espena/broadcast-clock/drawings/broadcast_clock_back.png

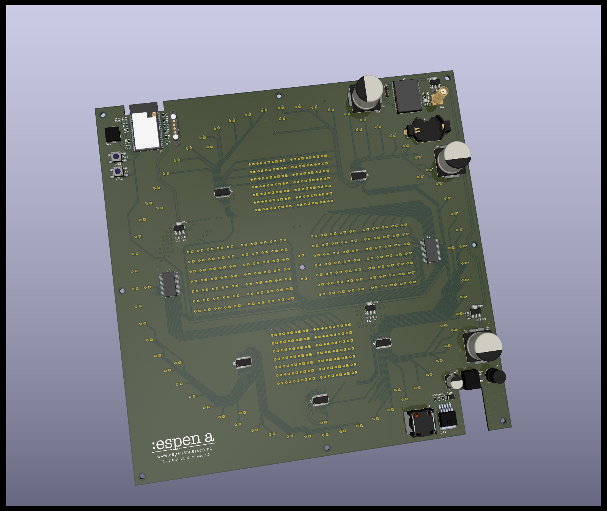
drawings/broadcast_clock_back.png
