espena/broadcast-clock/drawings/broadcast_clock_front.png

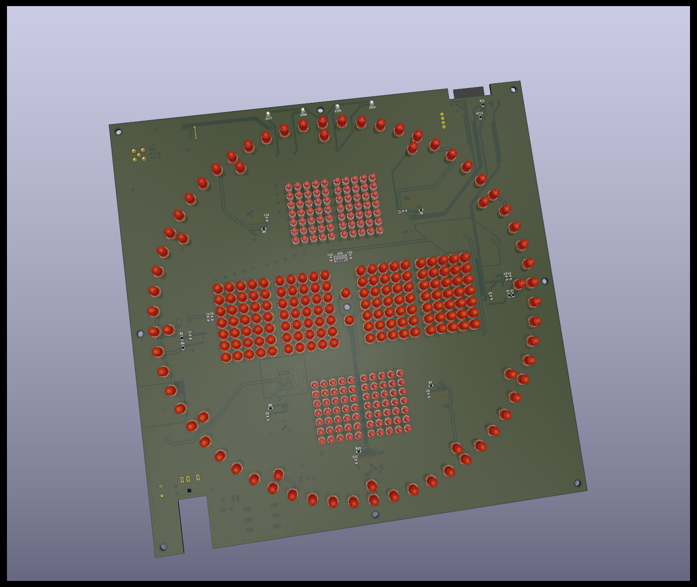
drawings/broadcast_clock_front.png
