espena/broadcast-clock/drawings/kicad_pcb_editor_screencap.png

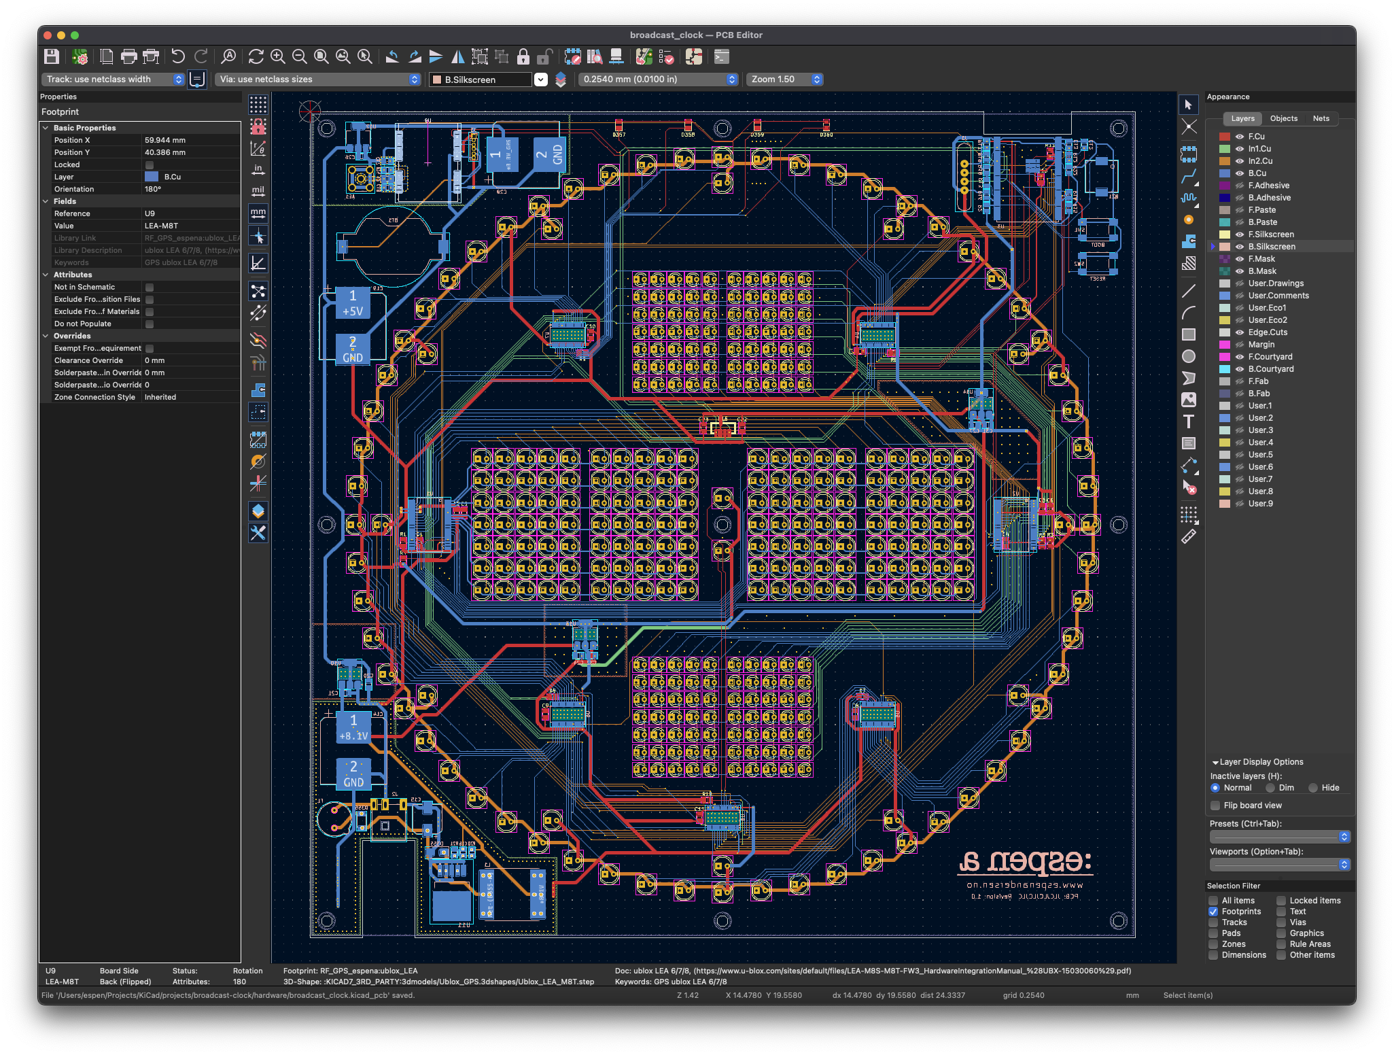
drawings/kicad_pcb_editor_screencap.png
