espena/broadcast-clock/drawings/qcad_panel_design.png

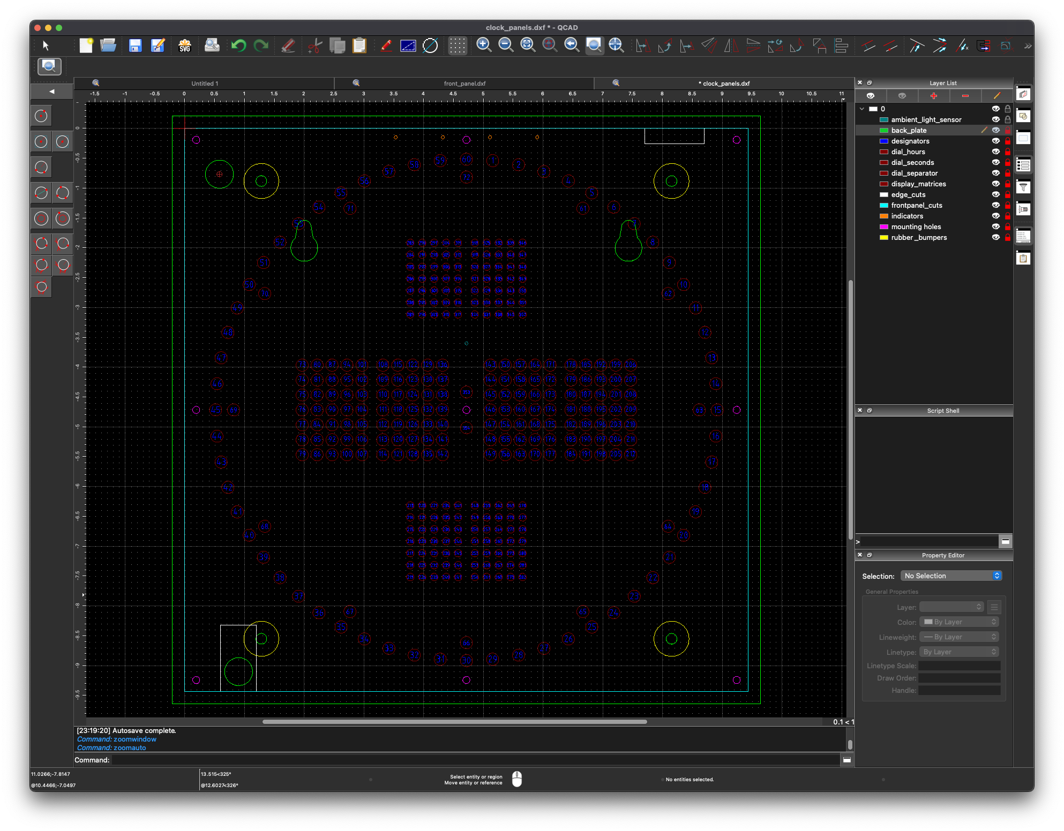
drawings/qcad_panel_design.png
