espena/broadcast-clock/drawings/schematics_png/max6952_schematic.png

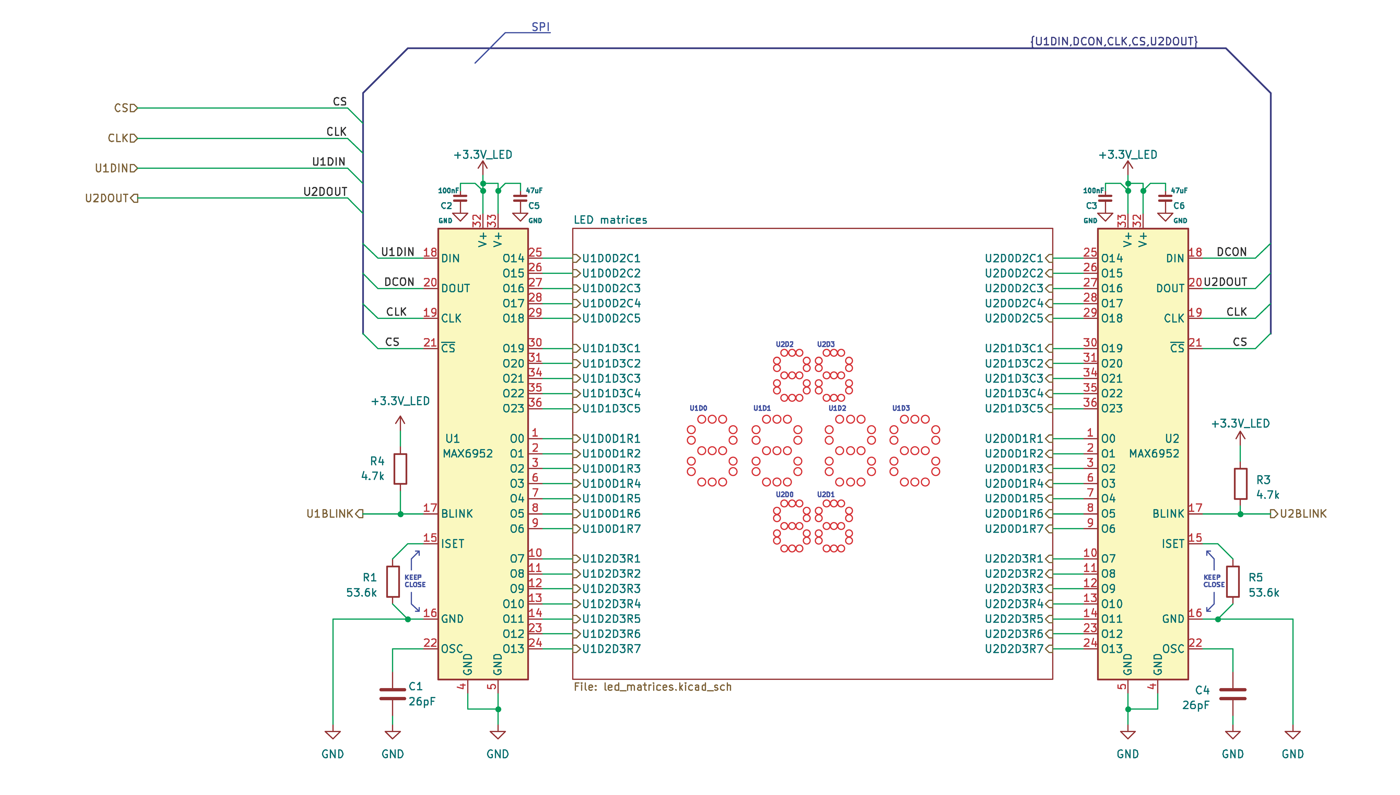
drawings/schematics_png/max6952_schematic.png
