espena/broadcast-clock/drawings/schematics_png/root_schematic.png

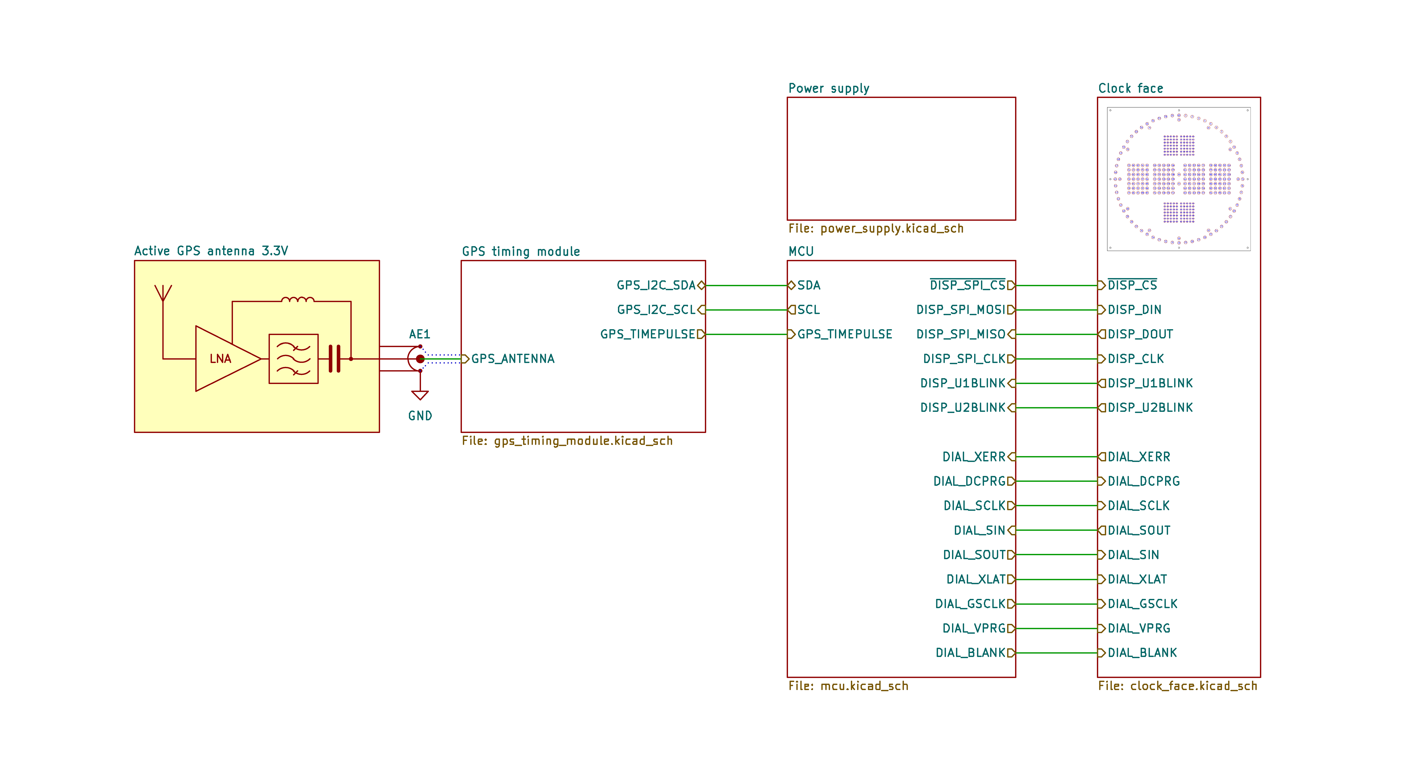
drawings/schematics_png/root_schematic.png
