espena/broadcast-clock/drawings/schematics_png/schematics_Page_3.png

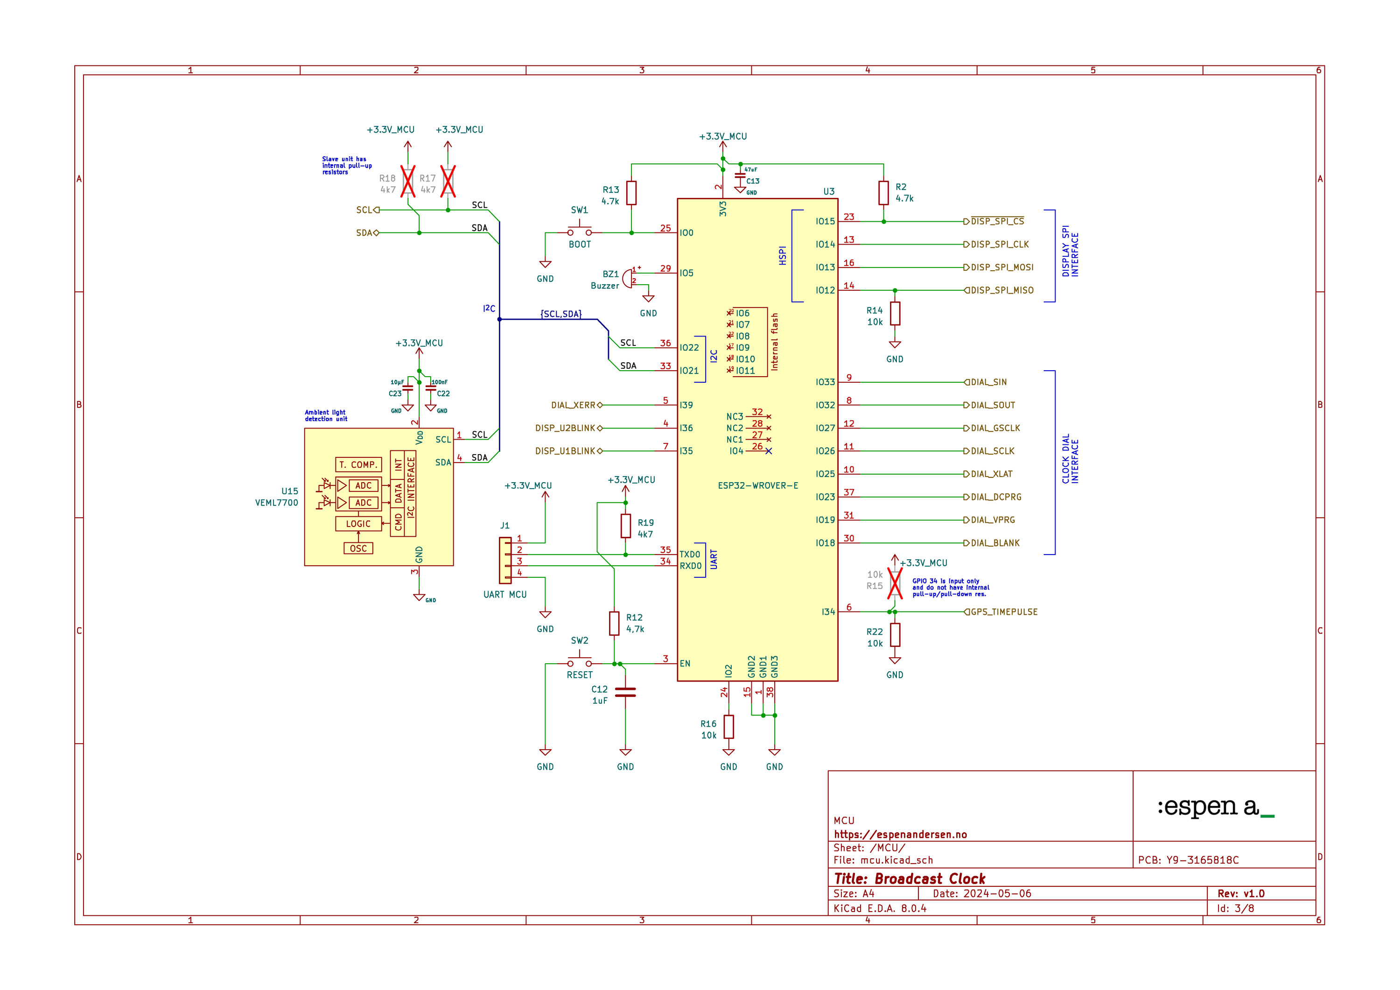
drawings/schematics_png/schematics_Page_3.png
