espena/broadcast-clock/drawings/schematics_png/schematics_Page_4.png

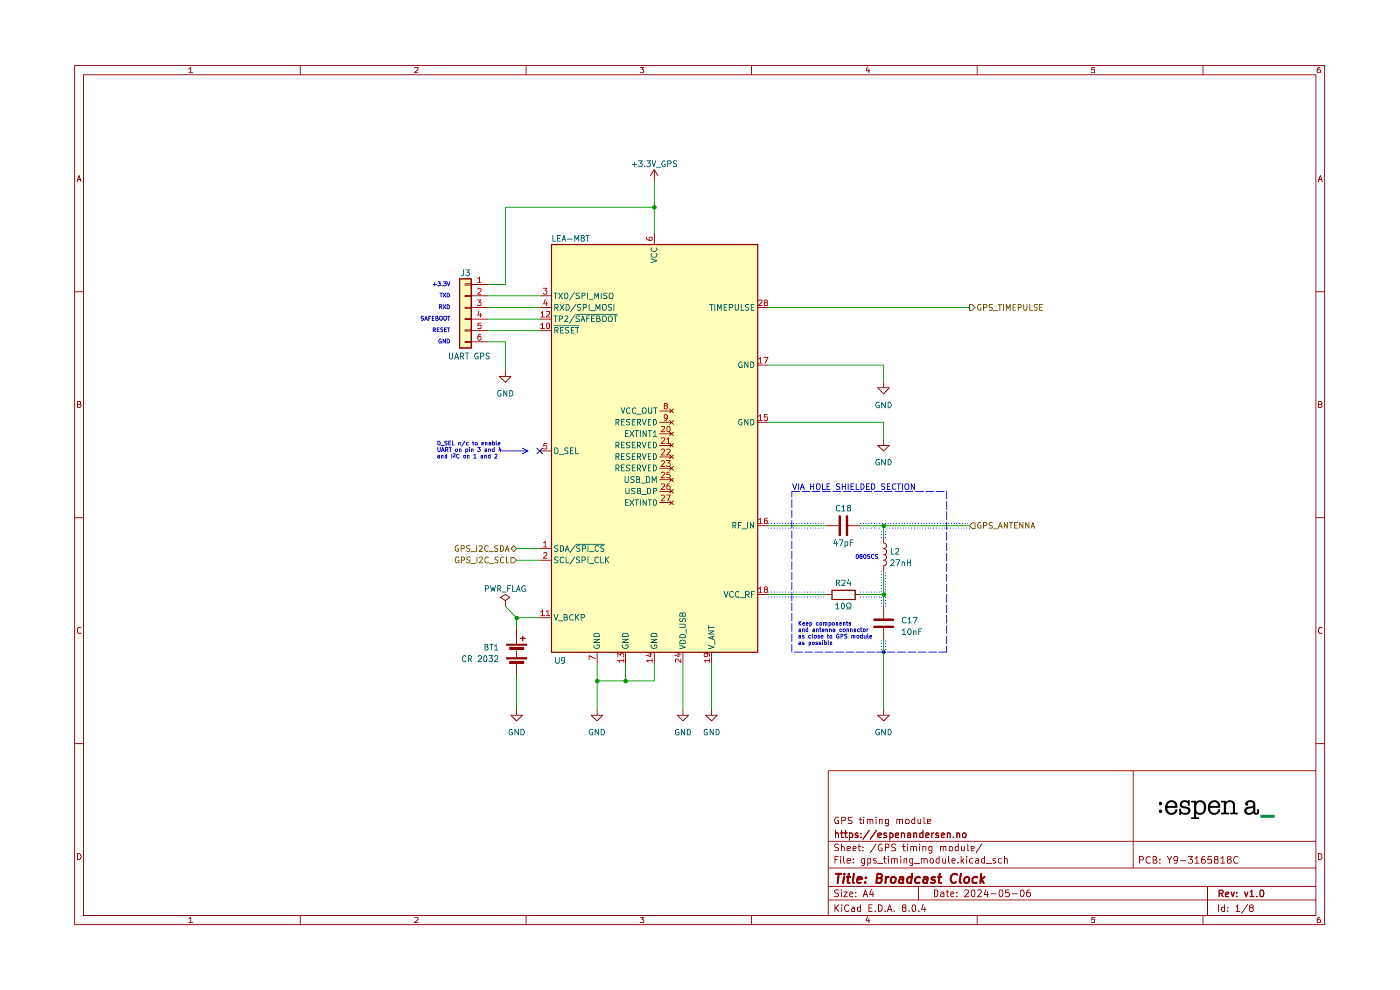
drawings/schematics_png/schematics_Page_4.png
