espena/broadcast-clock/drawings/schematics_png/schematics_Page_5.png

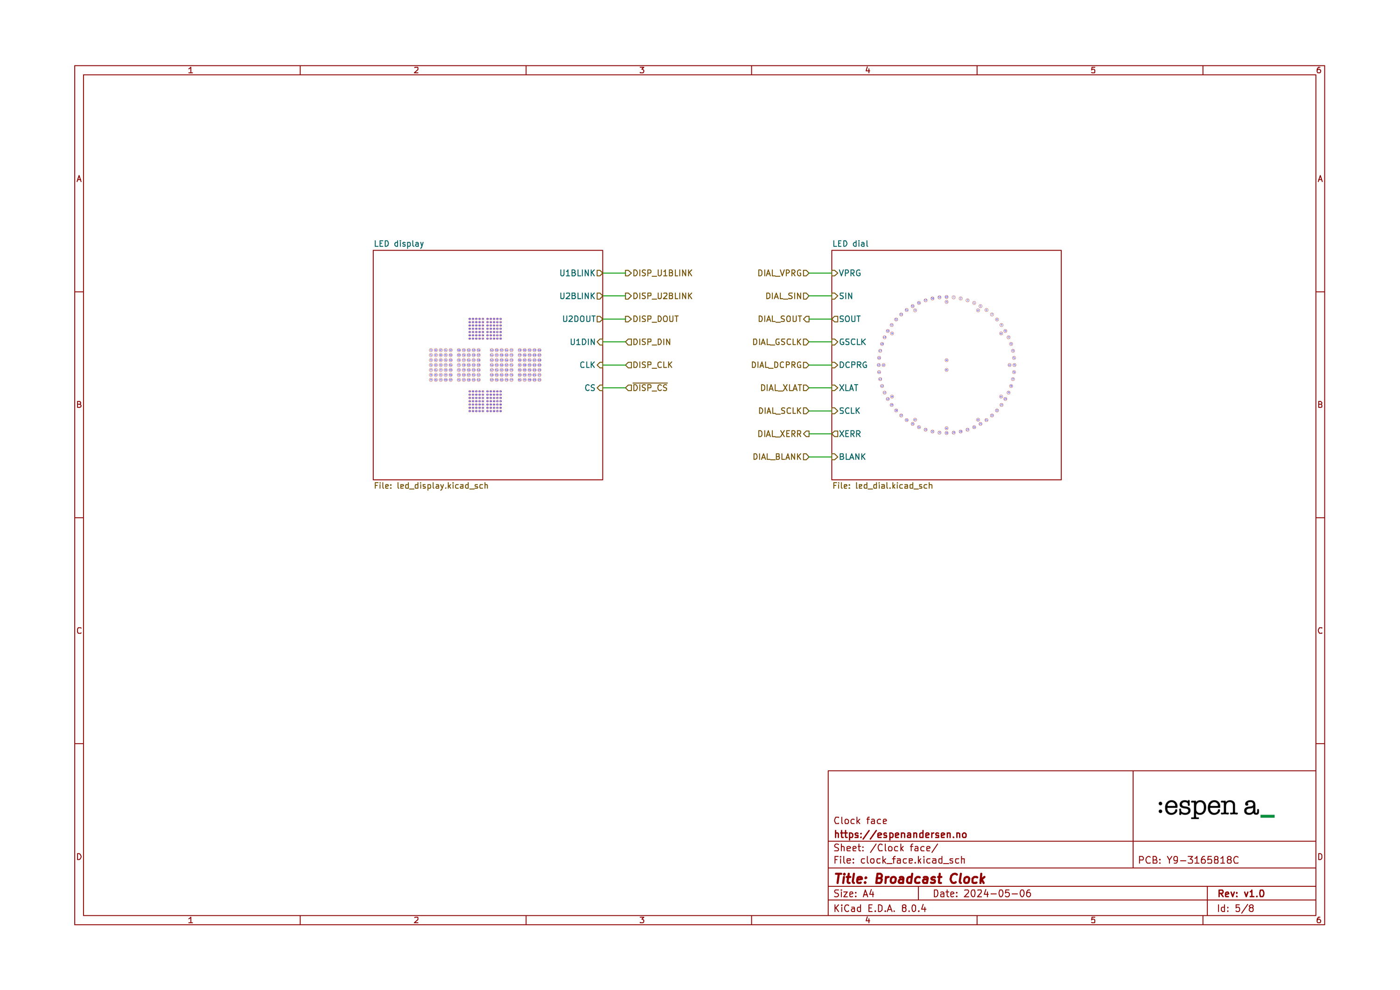
drawings/schematics_png/schematics_Page_5.png
