espena/broadcast-clock/drawings/schematics_png/schematics_Page_7.png

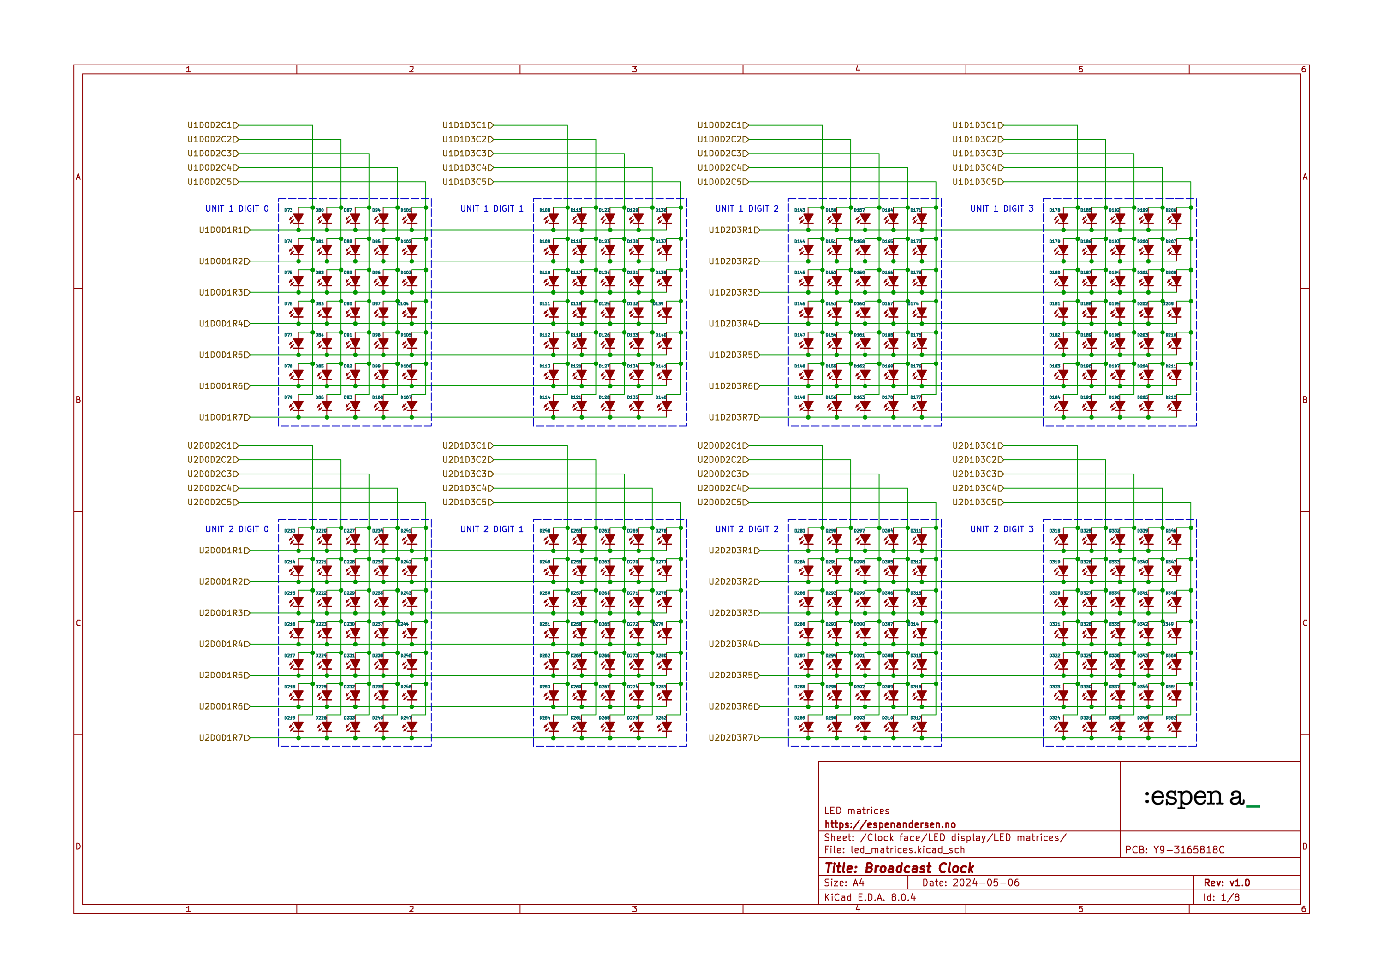
drawings/schematics_png/schematics_Page_7.png
