espena/broadcast-clock/drawings/schematics_png/tlc5940_schematic.png

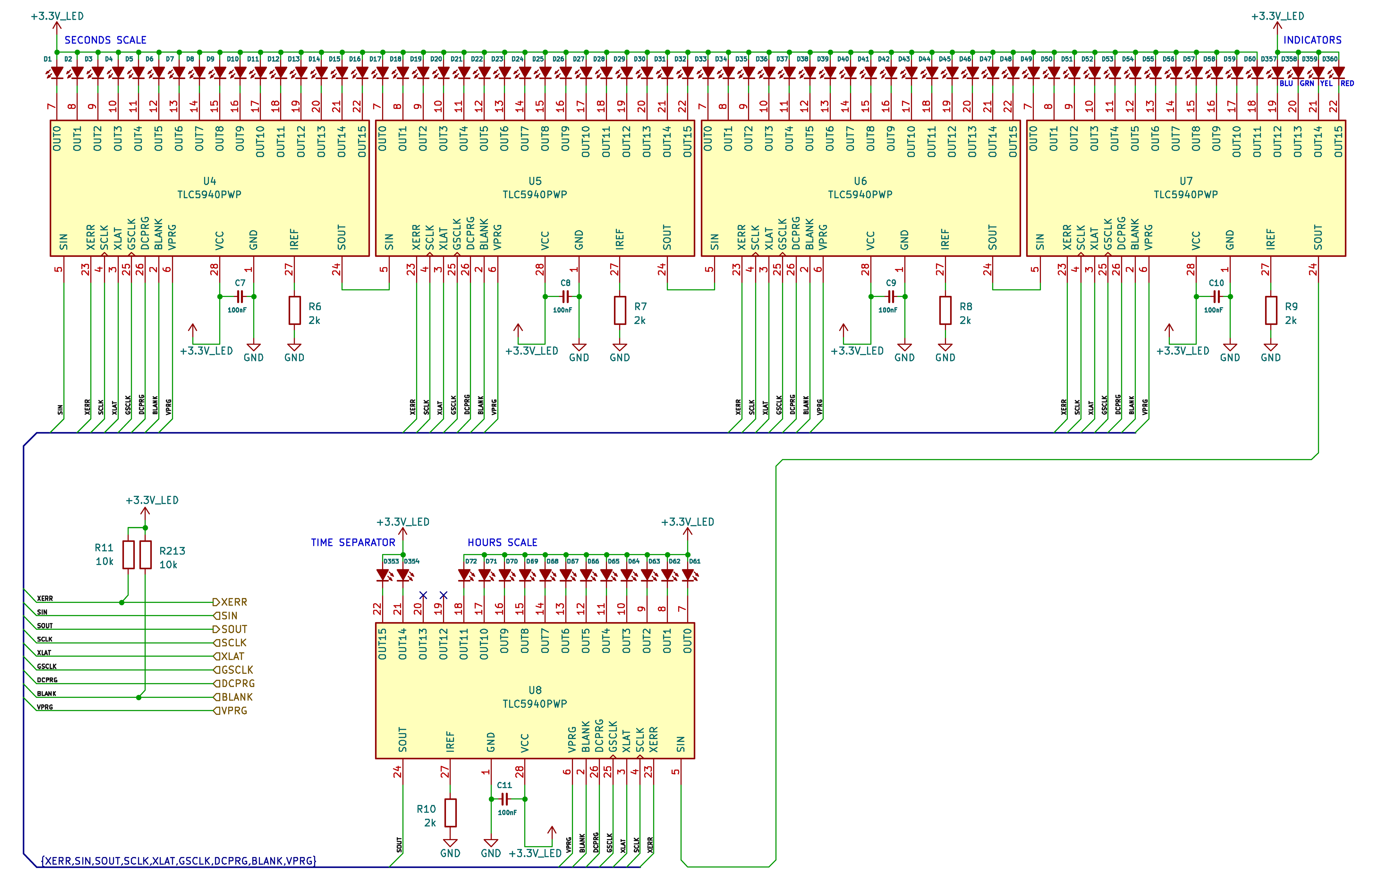
drawings/schematics_png/tlc5940_schematic.png
