espena/broadcast-clock/hardware/broadcast_clock-LED-Matrices.png

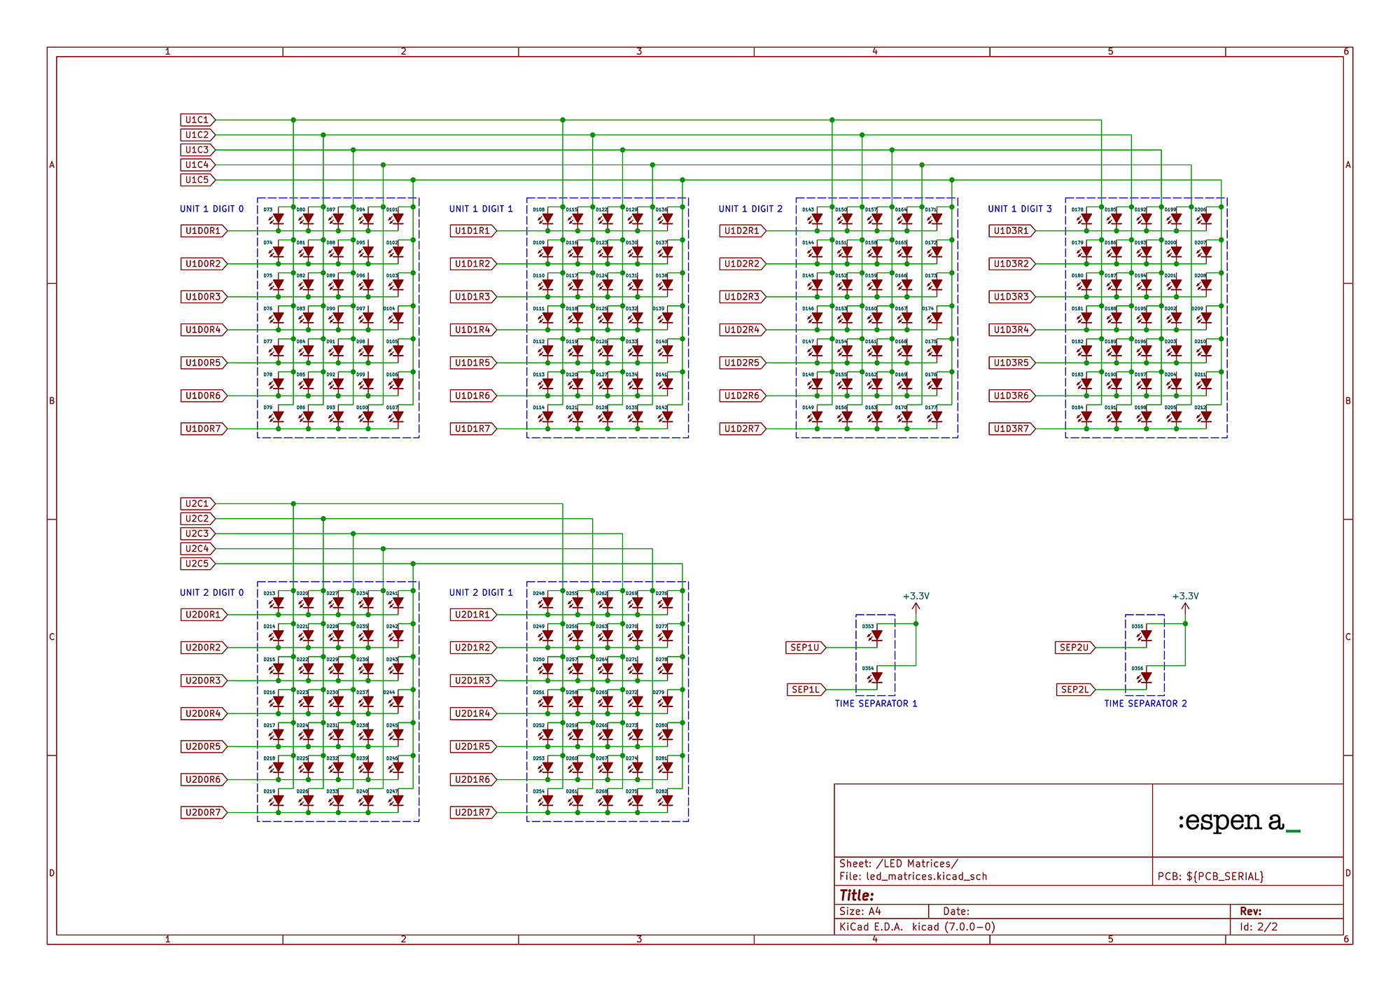
hardware/broadcast_clock-LED-Matrices.png
