espena/broadcast-clock/hardware/gfx/display.png

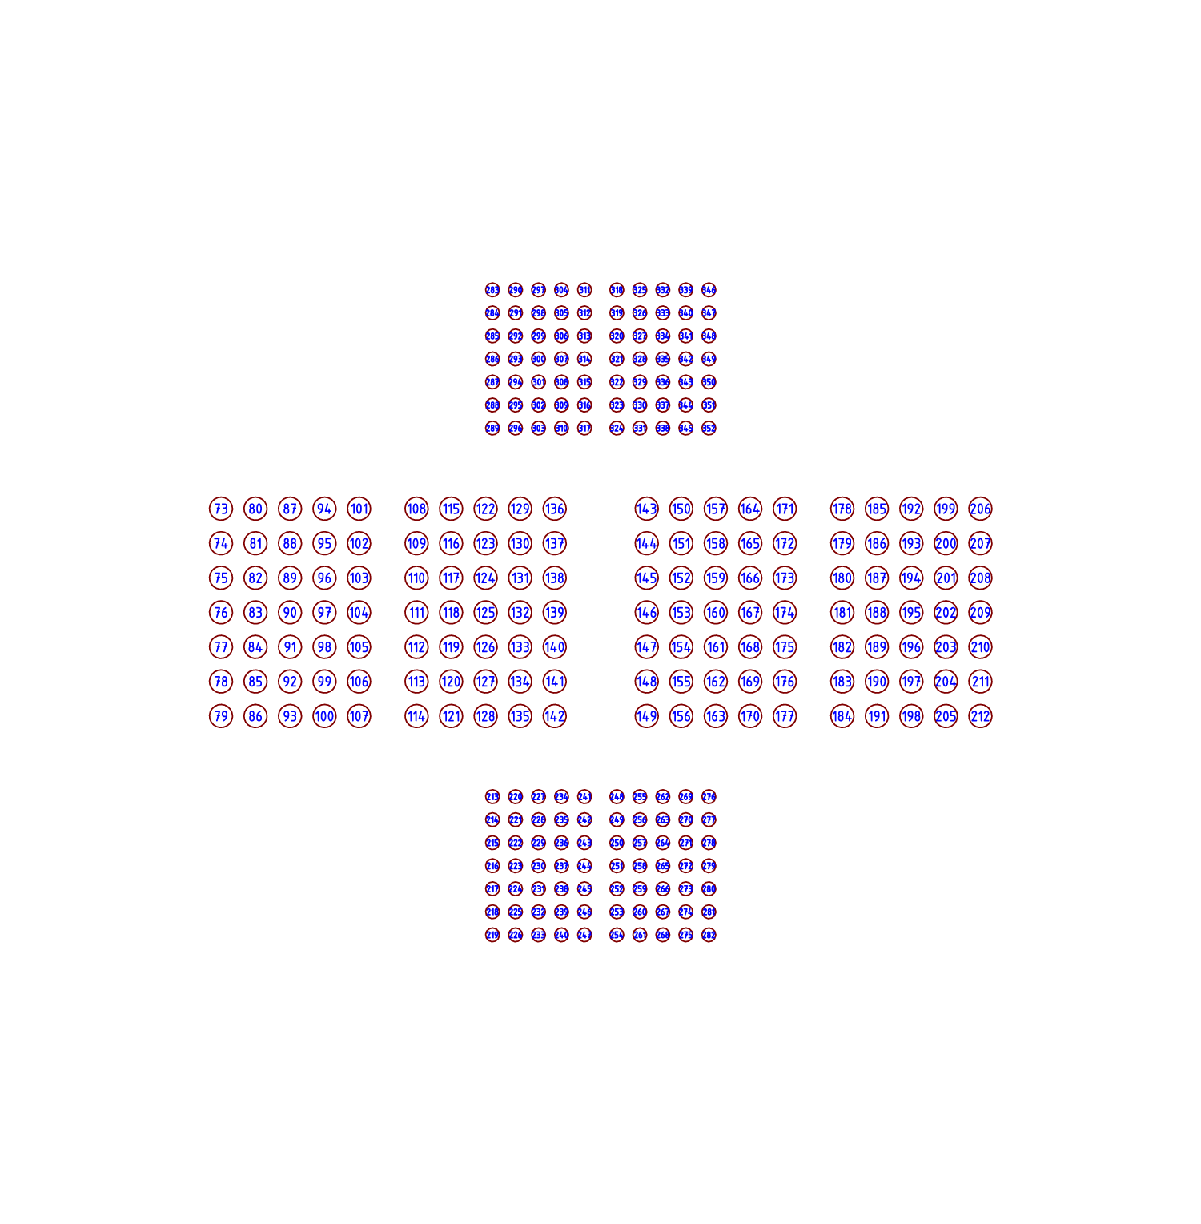
hardware/gfx/display.png
