espena/broadcast-clock/hardware/gfx/face_rendering.png

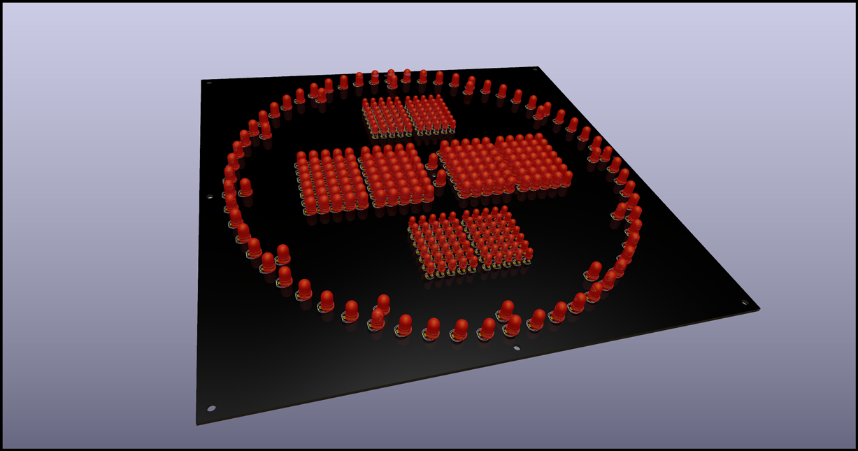
hardware/gfx/face_rendering.png
