espena/broadcast-clock/drawings/back_plate_measurements.png

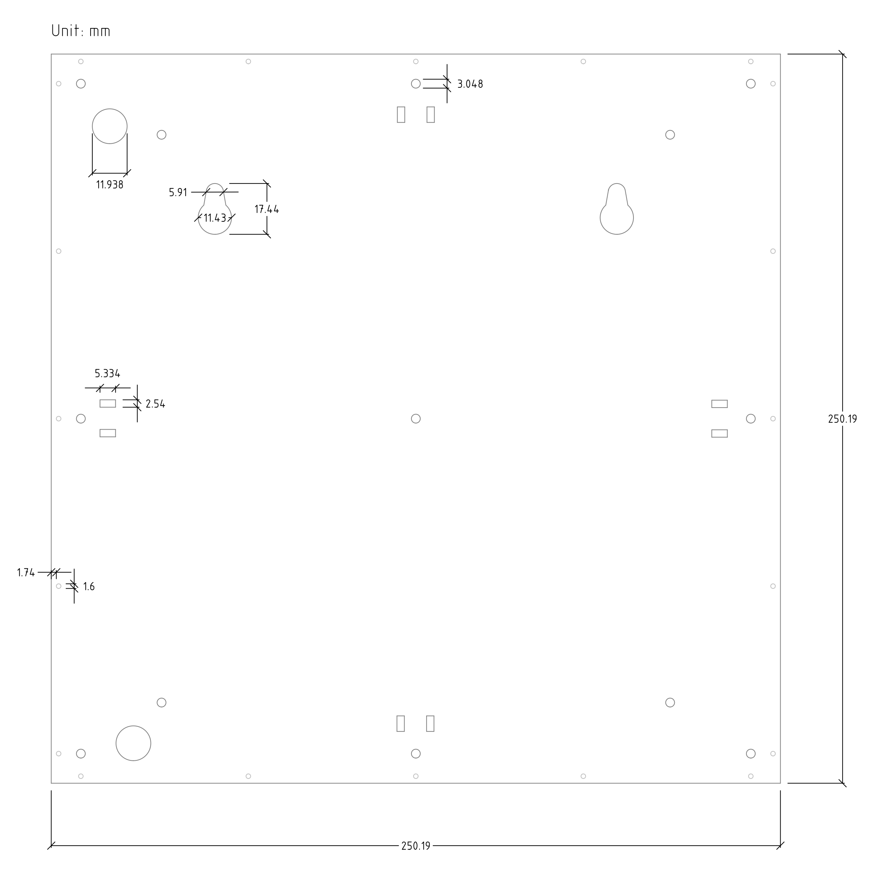
drawings/back_plate_measurements.png
