espena/broadcast-clock/firmware/broadcast-clock/main/components/application.cpp

#include "application.hpp"
#include "clock_face.hpp"
#include "captive_portal_dns.hpp"
#include "http_server.hpp"
#include "../gpio_mapping.hpp"
#include <rtc_wdt.h>
#include <string>
#include <memory.h>
#include <nvs_flash.h>
#include <esp_timer.h>
#include <esp_log.h>

using namespace espena::broadcast_clock;

const char *application::m_component_name = "application";

application::
application() : m_configuration( nullptr ),
                m_clock_status( m_clock_face.get_indicators() ),
                m_event_loop_handle( nullptr ) {

  esp_event_loop_args_t loop_args = {
    .queue_size = 100,
    .task_name = "event_loop",
    .task_priority = 15,
    .task_stack_size = 4096,
    .task_core_id = tskNO_AFFINITY
  };

  esp_event_loop_create( &loop_args, &m_event_loop_handle );
  m_clock_status.set_event_loop_handle( m_event_loop_handle );
}

application::
~application() {
}

void application::
init() {

    init_nvs();

    m_configuration = broadcast_clock::configuration::get_instance();
    m_configuration->set_event_loop_handle( m_event_loop_handle );

    init_timezone();
    init_i2c();

    esp_netif_init();
    esp_event_loop_create_default();

    m_http_server.set_event_loop_handle( m_event_loop_handle );
    m_http_server.set_gnss_state( &m_clock_status );

    esp_event_handler_register_with( m_event_loop_handle,
                                     broadcast_clock::http_server::m_event_base,
                                     broadcast_clock::http_server::EVENT_SAVE,
                                     wifi_event_handler,
                                     this );

    esp_event_handler_register_with( m_event_loop_handle,
                                     broadcast_clock::http_server::m_event_base,
                                     broadcast_clock::http_server::EVENT_CANCEL,
                                     wifi_event_handler,
                                     this );

    esp_event_handler_register_with( m_event_loop_handle,
                                     broadcast_clock::http_server::m_event_base,
                                     broadcast_clock::http_server::EVENT_START_TIME_MODE,
                                     wifi_event_handler,
                                     this );

    esp_event_handler_register_with( m_event_loop_handle,
                                     broadcast_clock::http_server::m_event_base,
                                     broadcast_clock::http_server::EVENT_STOP_TIME_MODE,
                                     wifi_event_handler,
                                     this );

    esp_event_handler_register_with( m_event_loop_handle,
                                     broadcast_clock::http_server::m_event_base,
                                     broadcast_clock::http_server::EVENT_CONFIGURATOR_START,
                                     wifi_event_handler,
                                     this );

    esp_event_handler_register_with( m_event_loop_handle,
                                     broadcast_clock::http_server::m_event_base,
                                     broadcast_clock::http_server::EVENT_CONFIGURATOR_STOP,
                                     wifi_event_handler,
                                     this );

    esp_event_handler_register_with( m_event_loop_handle,
                                    http_server::m_event_base,
                                    http_server::EVENT_REBOOT_CPU,
                                    wifi_event_handler,
                                    this );

    esp_event_handler_register_with( m_event_loop_handle,
                                    http_server::m_event_base,
                                    http_server::EVENT_REBOOT_GNSS,
                                    wifi_event_handler,
                                    this );

    m_wifi.set_event_loop_handle( m_event_loop_handle );
    m_wifi.init( wifi::mode::access_point );

    esp_event_handler_register_with( m_event_loop_handle,
                                     broadcast_clock::wifi::m_event_base,
                                     broadcast_clock::wifi::WIFI_EVENT_GOT_IP,
                                     wifi_event_handler,
                                     this );

    esp_event_handler_register_with( m_event_loop_handle,
                                     broadcast_clock::wifi::m_event_base,
                                     broadcast_clock::wifi::ENTER_CONFIG_MODE,
                                     wifi_event_handler,
                                     this );

    esp_event_handler_register_with( m_event_loop_handle,
                                     broadcast_clock::wifi::m_event_base,
                                     broadcast_clock::wifi::LEAVE_CONFIG_MODE,
                                     wifi_event_handler,
                                     this );

    esp_event_handler_register_with( m_event_loop_handle,
                                     broadcast_clock::wifi::m_event_base,
                                     broadcast_clock::wifi::WIFI_EVENT_NTP_SYNC,
                                     wifi_event_handler,
                                     this );

    esp_event_handler_register_with( m_event_loop_handle,
                                     broadcast_clock::wifi::m_event_base,
                                     broadcast_clock::wifi::WIFI_EVENT_NTP_SYNC_FAILED,
                                     wifi_event_handler,
                                     this );
    init_ap_duration_timeout();

    m_beeper.set_event_loop_handle( m_event_loop_handle );
    m_beeper.init();
    
    m_clock_face.set_event_loop_handle( m_event_loop_handle );

    m_clock_face.init();

    esp_event_handler_register_with( m_event_loop_handle,
                                     broadcast_clock::clock_face::m_event_base,
                                     broadcast_clock::clock_face::EVENT_COUNTDOWN_FINISH,
                                     wifi_event_handler,
                                     this );

    m_lea_m8t.set_event_loop_handle( m_event_loop_handle );

    esp_event_handler_register_with( m_event_loop_handle,
                                     broadcast_clock::lea_m8t::m_event_base,
                                     broadcast_clock::lea_m8t::GNSS_INSTALLED,
                                     wifi_event_handler,
                                     this );

    esp_event_handler_register_with( m_event_loop_handle,
                                     broadcast_clock::lea_m8t::m_event_base,
                                     broadcast_clock::lea_m8t::TIMEPULSE_PRESENT,
                                     wifi_event_handler,
                                     this );

    esp_event_handler_register_with( m_event_loop_handle,
                                     broadcast_clock::lea_m8t::m_event_base,
                                     broadcast_clock::lea_m8t::TIMEPULSE_ABSENT,
                                     wifi_event_handler,
                                     this );

    esp_event_handler_register_with( m_event_loop_handle,
                                     broadcast_clock::lea_m8t::m_event_base,
                                     broadcast_clock::lea_m8t::UBX_NAV_TIMEUTC,
                                     wifi_event_handler,
                                     this );

    esp_event_handler_register_with( m_event_loop_handle,
                                     broadcast_clock::lea_m8t::m_event_base,
                                     broadcast_clock::lea_m8t::NO_TIME_SYNC,
                                     wifi_event_handler,
                                     this );

    esp_event_handler_register_with( m_event_loop_handle,
                                     broadcast_clock::lea_m8t::m_event_base,
                                     broadcast_clock::lea_m8t::HIGH_ACCURACY,
                                     wifi_event_handler,
                                     this );

    esp_event_handler_register_with( m_event_loop_handle,
                                     broadcast_clock::lea_m8t::m_event_base,
                                     broadcast_clock::lea_m8t::LOWER_ACCURACY,
                                     wifi_event_handler,
                                     this );

    m_lea_m8t.init();

    m_ntp_server.set_event_loop_handle( m_event_loop_handle );

    if( m_configuration->get_bool( "configurator" ) ) {
      m_http_server.init();
      m_http_server.start();
    }
}

void application::
on_press_test( void *arg ) {

}

void application::
on_start_test( void *arg ) {
  if( gpio_get_level( GPIO_NUM_0 ) == 0 ) {
    application *app = static_cast<application *>( arg );
    app->m_clock_face.test();
  }
}

void application::
wifi_event_handler( void *handler_arg,
                    esp_event_base_t event_base,
                    int32_t event_id,
                    void *event_params )
{
  const std::string source = ( char * ) event_base;
  if( source == broadcast_clock::wifi::m_event_base ) {
    broadcast_clock::application *instance = static_cast<broadcast_clock::application *>( handler_arg );
    switch( event_id ) {
      case broadcast_clock::wifi::WIFI_EVENT_GOT_IP:
        instance->on_got_ip( static_cast<esp_netif_ip_info_t *>( event_params ) );
        break;
      case broadcast_clock::wifi::ENTER_CONFIG_MODE:
        instance->on_enter_config_mode();
        break;
      case broadcast_clock::wifi::LEAVE_CONFIG_MODE:
        instance->on_leave_config_mode();
        break;
      case broadcast_clock::wifi::WIFI_EVENT_NTP_SYNC:
        instance->m_clock_status.sntp_sync( true );
        break;
      case broadcast_clock::wifi::WIFI_EVENT_NTP_SYNC_FAILED:
        instance->m_clock_status.sntp_sync( false );
        break;
    }
  }
  else if( source == broadcast_clock::lea_m8t::m_event_base ) {
    broadcast_clock::application *instance = static_cast<broadcast_clock::application *>( handler_arg );
    switch( event_id ) {
      case broadcast_clock::lea_m8t::TIMEPULSE_PRESENT:
        instance->m_clock_status.gnss_timepulse( true );
        break;
      case broadcast_clock::lea_m8t::TIMEPULSE_ABSENT:
        instance->m_clock_status.gnss_timepulse( false );
        break;
      case broadcast_clock::lea_m8t::UBX_NAV_TIMEUTC:
        instance->m_clock_status.gnss_time_sync( true );
        break;
      case broadcast_clock::lea_m8t::NO_TIME_SYNC:
        instance->m_clock_status.gnss_time_sync( false );
        break;
      case broadcast_clock::lea_m8t::GNSS_INSTALLED:
        instance->m_clock_status.gnss_installed();
        break;
      case broadcast_clock::lea_m8t::HIGH_ACCURACY:
        instance->m_clock_status.high_accuracy( true, static_cast<int32_t *>( event_params ) );
        break;
      case broadcast_clock::lea_m8t::LOWER_ACCURACY:
        instance->m_clock_status.high_accuracy( false, static_cast<int32_t *>( event_params ) );
        break;
    }
  }
  else if( source == broadcast_clock::http_server::m_event_base ) {
    broadcast_clock::application *instance = static_cast<broadcast_clock::application *>( handler_arg );
    switch( event_id ) {
      case broadcast_clock::http_server::EVENT_SAVE:
        instance->on_save_config( std::string( ( char * ) event_params ) );
        break;
      case broadcast_clock::http_server::EVENT_CANCEL:
        instance->on_cancel_config( std::string( ( char * ) event_params ) );
        break;
      case broadcast_clock::http_server::EVENT_START_TIME_MODE:
        instance->m_lea_m8t.start_time_mode();
        break;
      case broadcast_clock::http_server::EVENT_STOP_TIME_MODE:
        instance->m_lea_m8t.stop_time_mode();
        break;
      case broadcast_clock::http_server::EVENT_CONFIGURATOR_START:
        instance->m_clock_status.configurator_enabled( true );
        break;
      case broadcast_clock::http_server::EVENT_CONFIGURATOR_STOP:
        instance->m_clock_status.configurator_enabled( false );
        break;
      case broadcast_clock::http_server::EVENT_REBOOT_GNSS:
        instance->m_clock_status.reboot();
        instance->m_lea_m8t.reset();
        vTaskDelay( 7500 / portTICK_PERIOD_MS );
        // fallthru
      case broadcast_clock::http_server::EVENT_REBOOT_CPU:
        esp_restart();
        break;
    }
  }
  else if( source == broadcast_clock::clock_face::m_event_base ) {
    broadcast_clock::application *instance = static_cast<broadcast_clock::application *>( handler_arg );
    switch( event_id ) {
      case broadcast_clock::clock_face::EVENT_COUNTDOWN_FINISH:
        instance->on_countdown_finish();
        break;
    }
  }
}

void application::
init_ap_duration_timeout() {
  esp_timer_create_args_t timer_args;
  memset( &timer_args, 0x00, sizeof( esp_timer_create_args_t ) );
  timer_args.callback = &application::on_ap_duration_timeout;
  timer_args.arg = this;
  timer_args.name = m_component_name;
  ESP_ERROR_CHECK( esp_timer_create( &timer_args, &m_ap_duration_timer ) );
  ESP_ERROR_CHECK( esp_timer_start_once( m_ap_duration_timer, 30000000 ) );
}

void application::
switch_to_station_mode() {
  wifi_mode_t mode;
  esp_wifi_get_mode( &mode );
  if( mode == WIFI_MODE_STA ) {
    return;
  }
  m_captive_portal_dns.stop();
  if( !m_configuration->get_bool( "configurator" ) ) {
    m_http_server.stop();
  }
  m_wifi.init( wifi::mode::station );
}

void application::
on_got_ip( esp_netif_ip_info_t *ip_info ) {
  m_clock_face.display_ip( ip_info );
  if( m_lea_m8t.present() ) {
    m_ntp_server.init();
  }
}

void application::
on_enter_config_mode() {
  if( m_ap_duration_timer ) {
    ESP_ERROR_CHECK( esp_timer_stop( m_ap_duration_timer ) );
    ESP_ERROR_CHECK( esp_timer_delete( m_ap_duration_timer ) );
    m_ap_duration_timer = nullptr;
    m_captive_portal_dns.init();
    m_captive_portal_dns.start();
    if( !m_configuration->get_bool( "configurator" ) ) {
      m_http_server.init();
      m_http_server.start();
    }
  }
}

void application::
on_save_config( std::string post_data ) {
  ESP_LOGI( "application", "Save config: %s", post_data.c_str() );
  switch_to_station_mode();
  m_configuration->update( post_data );
  init_timezone();
}

void application::
on_cancel_config( std::string post_data ) {
  switch_to_station_mode();
  init_timezone();
}

void application::
on_leave_config_mode() {
  switch_to_station_mode();
}

void application::
on_countdown_finish() {
  m_beeper.alarm();
}

void application::
on_ap_duration_timeout( void *arg ) {
  ESP_LOGI( "application", "Terminate access mode, start station mode" );
  application *app = static_cast<application *>( arg );
  app->m_wifi.init( wifi::mode::station );
}

void application::
init_nvs() {
  esp_err_t nvs_status = nvs_flash_init();
  if ( nvs_status == ESP_ERR_NVS_NO_FREE_PAGES ||
       nvs_status == ESP_ERR_NVS_NEW_VERSION_FOUND )
  {
    ESP_ERROR_CHECK( nvs_flash_erase() );
    nvs_status = nvs_flash_init();
  }
  ESP_ERROR_CHECK( nvs_status );
}

void application::
init_timezone() {
  std::string timezone = m_configuration->get_str( "time_zone" );
  ESP_LOGI( "application", "Setting timezone to %s", timezone.c_str() );
  setenv( "TZ", timezone.c_str(), 1 );
  tzset();
}

void application::
init_i2c() {
  i2c_config_t conf;
  memset( &conf, 0x00, sizeof( i2c_config_t ) );
  conf.mode = I2C_MODE_MASTER;
  conf.sda_io_num = I2C_SDA;
  conf.sda_pullup_en = GPIO_PULLUP_ENABLE;
  conf.scl_io_num = I2C_SCL;
  conf.scl_pullup_en = GPIO_PULLUP_ENABLE;
  conf.master.clk_speed = 400000;

  ESP_ERROR_CHECK( i2c_param_config( I2C_NUM_0, &conf ) );
  ESP_ERROR_CHECK( i2c_driver_install( I2C_NUM_0, I2C_MODE_MASTER, 0, 0, 0 ) );
  i2c_set_timeout( I2C_NUM_0, 1000000 );
}
